MichaelMGonzalez/MagneticFieldLocalization/CAD/3D_Parts/PhoneOutline.scad

use <PhoneMount.scad>;

cut_dim = [100,50,68.5];
difference() {
	FullStand();
	cube( cut_dim, true );
	translate( [0,0,70] )
	cube( cut_dim, true );
}
