MichaelMGonzalez/MagneticFieldLocalization/CAD/3D_Parts/ScrewMountTest.scad

use <PhoneMount.scad>;
ScrewMount(0,0,0);
