MichaelMGonzalez/MagneticFieldLocalization/MagneticFieldData/testrun1.csv

time | x | y | z | MF
0.009 | 2.52 | -36.48 | -5.70 | 37.01
0.014 | 2.46 | -36.54 | -5.70 | 37.06
0.024 | 2.46 | -36.54 | -5.70 | 37.06
0.033 | 2.46 | -36.54 | -5.70 | 37.06
0.043 | 2.46 | -36.60 | -5.70 | 37.12
0.065 | 2.46 | -36.60 | -5.76 | 37.13
0.066 | 2.46 | -36.60 | -5.76 | 37.13
0.096 | 2.46 | -36.60 | -5.76 | 37.13
0.097 | 2.46 | -36.60 | -5.76 | 37.13
0.098 | 2.46 | -36.66 | -5.76 | 37.19
0.105 | 2.46 | -36.66 | -5.76 | 37.19
0.121 | 2.52 | -36.66 | -5.76 | 37.20
0.138 | 2.58 | -36.66 | -5.76 | 37.20
0.139 | 2.58 | -36.66 | -5.76 | 37.20
0.154 | 2.64 | -36.66 | -5.76 | 37.20
0.155 | 2.70 | -36.66 | -5.70 | 37.20
0.172 | 2.70 | -36.66 | -5.70 | 37.20
0.173 | 2.70 | -36.66 | -5.70 | 37.20
0.206 | 2.70 | -36.60 | -5.70 | 37.14
0.207 | 2.70 | -36.66 | -5.64 | 37.19
0.208 | 2.64 | -36.66 | -5.64 | 37.19
0.222 | 2.58 | -36.66 | -5.64 | 37.18
0.223 | 2.52 | -36.66 | -5.64 | 37.18
0.239 | 2.46 | -36.66 | -5.64 | 37.17
0.256 | 2.40 | -36.66 | -5.64 | 37.17
0.257 | 2.34 | -36.66 | -5.64 | 37.17
0.273 | 2.34 | -36.66 | -5.64 | 37.17
0.274 | 2.28 | -36.66 | -5.58 | 37.15
0.305 | 2.34 | -36.66 | -5.52 | 37.15
0.307 | 2.34 | -36.66 | -5.46 | 37.14
0.307 | 2.34 | -36.66 | -5.46 | 37.14
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
