MichaelMGonzalez/MagneticFieldLocalization/MagneticFieldData/testrun3.csv

time | x | y | z | MF
0.013 | 2.70 | -37.02 | -5.46 | 37.52
0.014 | 2.70 | -37.02 | -5.46 | 37.52
0.025 | 2.70 | -37.02 | -5.46 | 37.52
0.037 | 2.70 | -37.02 | -5.52 | 37.53
0.055 | 2.70 | -37.02 | -5.52 | 37.53
0.055 | 2.70 | -37.02 | -5.52 | 37.53
0.071 | 2.70 | -37.02 | -5.52 | 37.53
0.072 | 2.70 | -37.02 | -5.52 | 37.53
0.089 | 2.70 | -37.02 | -5.52 | 37.53
0.089 | 2.70 | -37.02 | -5.52 | 37.53
0.108 | 2.70 | -37.02 | -5.58 | 37.54
0.111 | 2.70 | -37.02 | -5.58 | 37.54
0.145 | 2.70 | -37.02 | -5.58 | 37.54
0.148 | 2.70 | -37.02 | -5.58 | 37.54
0.148 | 2.70 | -37.02 | -5.58 | 37.54
0.149 | 2.82 | -37.02 | -5.58 | 37.54
0.176 | 2.94 | -37.02 | -5.52 | 37.54
0.177 | 3.06 | -37.02 | -5.52 | 37.55
0.178 | 3.12 | -36.96 | -5.52 | 37.50
0.190 | 3.24 | -36.96 | -5.46 | 37.50
0.207 | 3.36 | -36.96 | -5.46 | 37.51
0.208 | 3.42 | -36.96 | -5.40 | 37.51
0.235 | 3.48 | -36.96 | -5.40 | 37.51
0.236 | 3.48 | -36.90 | -5.34 | 37.45
0.244 | 3.36 | -36.90 | -5.34 | 37.44
0.259 | 3.24 | -36.96 | -5.28 | 37.48
0.260 | 3.18 | -36.96 | -5.28 | 37.47
0.274 | 3.06 | -37.02 | -5.28 | 37.52
0.291 | 2.94 | -37.02 | -5.28 | 37.51
0.293 | 2.76 | -37.14 | -5.28 | 37.61
0.308 | 2.64 | -37.20 | -5.28 | 37.67
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
