MichaelMGonzalez/MagneticFieldLocalization/MagneticFieldLocalizer/app/src/main/java/com/ashmp/magneticfieldlocalizer/activity/SerialConsoleActivity.java

/* Copyright 2011-2013 Google Inc.
 * Copyright 2013 mike wakerly <opensource@hoho.com>
 *
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
 * Project home page: https://github.com/mik3y/usb-serial-for-android
 */

package com.ashmp.magneticfieldlocalizer.activity;

import android.app.Activity;
import android.content.Context;
import android.content.Intent;
import android.hardware.usb.UsbDeviceConnection;
import android.hardware.usb.UsbManager;
import android.os.Bundle;
import android.util.Log;
import android.view.View;
import android.widget.AdapterView;
import android.widget.ArrayAdapter;
import android.widget.CheckBox;
import android.widget.CompoundButton;
import android.widget.ScrollView;
import android.widget.Spinner;
import android.widget.TextView;

import usbserial.driver.UsbSerialPort;
import usbserial.util.HexDump;
import usbserial.util.SerialInputOutputManager;

import java.io.IOException;
import java.util.HashMap;
import java.util.concurrent.ExecutorService;
import java.util.concurrent.Executors;

import com.ashmp.magneticfieldlocalizer.R;
import com.ashmp.magneticfieldlocalizer.SerialMsgHeader;



/**
 * Monitors a single {@link UsbSerialPort} instance, showing all data
 * received.
 *
 * @author mike wakerly (opensource@hoho.com)
 */
public class SerialConsoleActivity extends Activity implements AdapterView.OnItemSelectedListener{

    private final String TAG = SerialConsoleActivity.class.getSimpleName();

    /**
     * Driver instance, passed in statically via
     * {@link #show(Context, UsbSerialPort)}.
     *
     * <p/>
     * This is a devious hack; it'd be cleaner to re-create the driver using
     * arguments passed in with the {@link #startActivity(Intent)} intent. We
     * can get away with it because both activities will run in the same
     * process, and this is a simple demo.
     */
    private static UsbSerialPort sPort = null;

    private TextView mTitleTextView;
    private TextView mDumpTextView;
    private Spinner msgSpinner;
    private ScrollView mScrollView;
    private CheckBox chkDTR;
    private CheckBox chkRTS;

    private final ExecutorService mExecutor = Executors.newSingleThreadExecutor();
    private HashMap<String, Byte> msgMap;

    private SerialInputOutputManager mSerialIoManager;

    private final SerialInputOutputManager.Listener mListener =
            new SerialInputOutputManager.Listener() {

        @Override
        public void onRunError(Exception e) {
            Log.d(TAG, "Runner stopped.");
        }

        @Override
        public void onNewData(final byte[] data) {
            SerialConsoleActivity.this.runOnUiThread(new Runnable() {
                @Override
                public void run() {
                    SerialConsoleActivity.this.updateReceivedData(data);
                }
            });
        }
    };

    @Override
    public void onCreate(Bundle savedInstanceState) {
        super.onCreate(savedInstanceState);
        setContentView(R.layout.serial_console);
        mTitleTextView = (TextView) findViewById(R.id.demoTitle);
        mDumpTextView = (TextView) findViewById(R.id.consoleText);
        mScrollView = (ScrollView) findViewById(R.id.demoScroller);
        chkDTR = (CheckBox) findViewById(R.id.checkBoxDTR);
        chkRTS = (CheckBox) findViewById(R.id.checkBoxRTS);
        initMsgContainers();

        chkDTR.setOnCheckedChangeListener(new CompoundButton.OnCheckedChangeListener() {
            @Override
            public void onCheckedChanged(CompoundButton buttonView, boolean isChecked) {
                try {
                    sPort.setDTR(isChecked);
                }catch (IOException x){}
            }
        });

        chkRTS.setOnCheckedChangeListener(new CompoundButton.OnCheckedChangeListener() {
            @Override
            public void onCheckedChanged(CompoundButton buttonView, boolean isChecked) {
                try {
                    sPort.setRTS(isChecked);
                }catch (IOException x){}
            }
        });

    }


    @Override
    protected void onPause() {
        super.onPause();
        stopIoManager();
        if (sPort != null) {
            try {
                sPort.close();
            } catch (IOException e) {
                // Ignore.
            }
            sPort = null;
        }
        finish();
    }

    void showStatus(TextView theTextView, String theLabel, boolean theValue){
        String msg = theLabel + ": " + (theValue ? "enabled" : "disabled") + "\n";
        theTextView.append(msg);
    }

    private void initMsgContainers() {
        // Setup the hashmap
        msgMap = new HashMap<>(SerialMsgHeader.MSG_KEYS.length);
        for( int i = 0; i < SerialMsgHeader.MSG_KEYS.length; i++)
            msgMap.put(SerialMsgHeader.MSG_KEYS[i], SerialMsgHeader.MSG_VALS[i]);
        // Setup the spinner
        msgSpinner = (Spinner) findViewById(R.id.msgSpinner);
        ArrayAdapter<String> adapter = new ArrayAdapter<String>(this,
                android.R.layout.simple_spinner_dropdown_item, SerialMsgHeader.MSG_KEYS);
        msgSpinner.setAdapter(adapter);
        msgSpinner.setOnItemSelectedListener(this);
    }

    @Override
    protected void onResume() {
        super.onResume();
        Log.d(TAG, "Resumed, port=" + sPort);
        if (sPort == null) {
            mTitleTextView.setText("No serial device.");
        } else {
            final UsbManager usbManager = (UsbManager) getSystemService(Context.USB_SERVICE);

            UsbDeviceConnection connection = usbManager.openDevice(sPort.getDriver().getDevice());
            if (connection == null) {
                mTitleTextView.setText("Opening device failed");
                return;
            }

            try {
                sPort.open(connection);
                sPort.setParameters(SerialMsgHeader.BAUD_RATE, 8, UsbSerialPort.STOPBITS_1, UsbSerialPort.PARITY_NONE);

                showStatus(mDumpTextView, "CD  - Carrier Detect", sPort.getCD());
                showStatus(mDumpTextView, "CTS - Clear To Send", sPort.getCTS());
                showStatus(mDumpTextView, "DSR - Data Set Ready", sPort.getDSR());
                showStatus(mDumpTextView, "DTR - Data Terminal Ready", sPort.getDTR());
                showStatus(mDumpTextView, "DSR - Data Set Ready", sPort.getDSR());
                showStatus(mDumpTextView, "RI  - Ring Indicator", sPort.getRI());
                showStatus(mDumpTextView, "RTS - Request To Send", sPort.getRTS());

            } catch (IOException e) {
                Log.e(TAG, "Error setting up device: " + e.getMessage(), e);
                mTitleTextView.setText("Error opening device: " + e.getMessage());
                try {
                    sPort.close();
                } catch (IOException e2) {
                    // Ignore.
                }
                sPort = null;
                return;
            }
            mTitleTextView.setText("Serial device: " + sPort.getClass().getSimpleName());
        }
        onDeviceStateChange();
    }

    private void stopIoManager() {
        if (mSerialIoManager != null) {
            Log.i(TAG, "Stopping io manager ..");
            mSerialIoManager.stop();
            mSerialIoManager = null;
        }
    }

    private void startIoManager() {
        if (sPort != null) {
            Log.i(TAG, "Starting io manager ..");
            mSerialIoManager = new SerialInputOutputManager(sPort, mListener);
            mExecutor.submit(mSerialIoManager);
        }
    }

    private void onDeviceStateChange() {
        stopIoManager();
        startIoManager();
    }

    private void updateReceivedData(byte[] data) {
        final String message = "Read " + data.length + " bytes: \n"
                + HexDump.dumpHexString(data) + "\n\n";
        mDumpTextView.append(message);
        mScrollView.smoothScrollTo(0, mDumpTextView.getBottom());
    }

    /**
     * Starts the activity, using the supplied driver instance.
     *
     * @param context
     * @param driver
     */
    static void show(Context context, UsbSerialPort port) {
        sPort = port;
        final Intent intent = new Intent(context, SerialConsoleActivity.class);
        intent.addFlags(Intent.FLAG_ACTIVITY_SINGLE_TOP | Intent.FLAG_ACTIVITY_NO_HISTORY);
        context.startActivity(intent);
    }

    @Override
    public void onItemSelected(AdapterView<?> parent, View view, int position, long id) {
        byte[] msgBuffer = { SerialMsgHeader.MSG_VALS[position] };
        try {
            sPort.write(msgBuffer, 1000);
        } catch (IOException e) {
            e.printStackTrace();
        }
    }

    @Override
    public void onNothingSelected(AdapterView<?> parent) {

    }
}
