MichaelMGonzalez/MagneticFieldLocalization/MagneticFieldLocalizer/app/src/main/java/com/ashmp/magneticfieldlocalizer/activity/DeviceListActivity.java

/* Copyright 2011-2013 Google Inc.
 * Copyright 2013 mike wakerly <opensource@hoho.com>
 *
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
 * Project home page: https://github.com/mik3y/usb-serial-for-android
 */

package com.ashmp.magneticfieldlocalizer.activity;

import android.app.Activity;
import android.content.Context;
import android.hardware.usb.UsbDevice;
import android.hardware.usb.UsbManager;
import android.os.AsyncTask;
import android.os.Bundle;
import android.os.Handler;
import android.os.Message;
import android.os.SystemClock;
import android.util.Log;
import android.view.LayoutInflater;
import android.view.View;
import android.view.ViewGroup;
import android.widget.AdapterView;
import android.widget.ArrayAdapter;
import android.widget.ListView;
import android.widget.ProgressBar;
import android.widget.TextView;
import android.widget.TwoLineListItem;

import com.ashmp.magneticfieldlocalizer.R;

import usbserial.driver.UsbSerialDriver;
import usbserial.driver.UsbSerialPort;
import usbserial.driver.UsbSerialProber;
import usbserial.util.HexDump;

import java.util.ArrayList;
import java.util.List;

/**
 * Shows a {@link ListView} of available USB devices.
 *
 * @author mike wakerly (opensource@hoho.com)
 */
public class DeviceListActivity extends Activity {

    private final String TAG = DeviceListActivity.class.getSimpleName();

    private UsbManager mUsbManager;
    private ListView mListView;
    private TextView mProgressBarTitle;
    private ProgressBar mProgressBar;

    private static final int MESSAGE_REFRESH = 101;
    private static final long REFRESH_TIMEOUT_MILLIS = 5000;

    private final Handler mHandler = new Handler() {
        @Override
        public void handleMessage(Message msg) {
            switch (msg.what) {
                case MESSAGE_REFRESH:
                    refreshDeviceList();
                    mHandler.sendEmptyMessageDelayed(MESSAGE_REFRESH, REFRESH_TIMEOUT_MILLIS);
                    break;
                default:
                    super.handleMessage(msg);
                    break;
            }
        }

    };

    private List<UsbSerialPort> mEntries = new ArrayList<UsbSerialPort>();
    private ArrayAdapter<UsbSerialPort> mAdapter;

    @Override
    public void onCreate(Bundle savedInstanceState) {
        super.onCreate(savedInstanceState);
        setContentView(R.layout.main);

        mUsbManager = (UsbManager) getSystemService(Context.USB_SERVICE);
        mListView = (ListView) findViewById(R.id.deviceList);
        mProgressBar = (ProgressBar) findViewById(R.id.progressBar);
        mProgressBarTitle = (TextView) findViewById(R.id.progressBarTitle);

        mAdapter = new ArrayAdapter<UsbSerialPort>(this,
                android.R.layout.simple_expandable_list_item_2, mEntries) {
            @Override
            public View getView(int position, View convertView, ViewGroup parent) {
                final TwoLineListItem row;
                if (convertView == null) {
                    final LayoutInflater inflater =
                            (LayoutInflater) getSystemService(Context.LAYOUT_INFLATER_SERVICE);
                    row = (TwoLineListItem) inflater.inflate(android.R.layout.simple_list_item_2, null);
                } else {
                    row = (TwoLineListItem) convertView;
                }

                final UsbSerialPort port = mEntries.get(position);
                final UsbSerialDriver driver = port.getDriver();
                final UsbDevice device = driver.getDevice();

                final String title = String.format("Vendor %s Product %s",
                        HexDump.toHexString((short) device.getVendorId()),
                        HexDump.toHexString((short) device.getProductId()));
                row.getText1().setText(title);

                final String subtitle = driver.getClass().getSimpleName();
                row.getText2().setText(subtitle);

                return row;
            }

        };
        mListView.setAdapter(mAdapter);

        mListView.setOnItemClickListener(new ListView.OnItemClickListener() {
            @Override
            public void onItemClick(AdapterView<?> parent, View view, int position, long id) {
                Log.d(TAG, "Pressed item " + position);
                if (position >= mEntries.size()) {
                    Log.w(TAG, "Illegal position.");
                    return;
                }

                final UsbSerialPort port = mEntries.get(position);
                showConsoleActivity(port);
            }
        });
    }

    @Override
    protected void onResume() {
        super.onResume();
        mHandler.sendEmptyMessage(MESSAGE_REFRESH);
    }

    @Override
    protected void onPause() {
        super.onPause();
        mHandler.removeMessages(MESSAGE_REFRESH);
    }

    private void refreshDeviceList() {
        showProgressBar();

        new AsyncTask<Void, Void, List<UsbSerialPort>>() {
            @Override
            protected List<UsbSerialPort> doInBackground(Void... params) {
                Log.d(TAG, "Refreshing device list ...");
                SystemClock.sleep(1000);

                final List<UsbSerialDriver> drivers =
                        UsbSerialProber.getDefaultProber().findAllDrivers(mUsbManager);

                final List<UsbSerialPort> result = new ArrayList<UsbSerialPort>();
                for (final UsbSerialDriver driver : drivers) {
                    final List<UsbSerialPort> ports = driver.getPorts();
                    Log.d(TAG, String.format("+ %s: %s port%s",
                            driver, Integer.valueOf(ports.size()), ports.size() == 1 ? "" : "s"));
                    result.addAll(ports);
                }

                return result;
            }

            @Override
            protected void onPostExecute(List<UsbSerialPort> result) {
                mEntries.clear();
                mEntries.addAll(result);
                mAdapter.notifyDataSetChanged();
                mProgressBarTitle.setText(
                        String.format("%s device(s) found",Integer.valueOf(mEntries.size())));
                hideProgressBar();
                Log.d(TAG, "Done refreshing, " + mEntries.size() + " entries found.");
            }

        }.execute((Void) null);
    }

    private void showProgressBar() {
        mProgressBar.setVisibility(View.VISIBLE);
        mProgressBarTitle.setText(R.string.refreshing);
    }

    private void hideProgressBar() {
        mProgressBar.setVisibility(View.INVISIBLE);
    }

    private void showConsoleActivity(UsbSerialPort port) {
        SerialConsoleActivity.show(this, port);
    }

}
